shabaz123/easyL1105/easyl1105-sch-jpeg-rev1.jpg

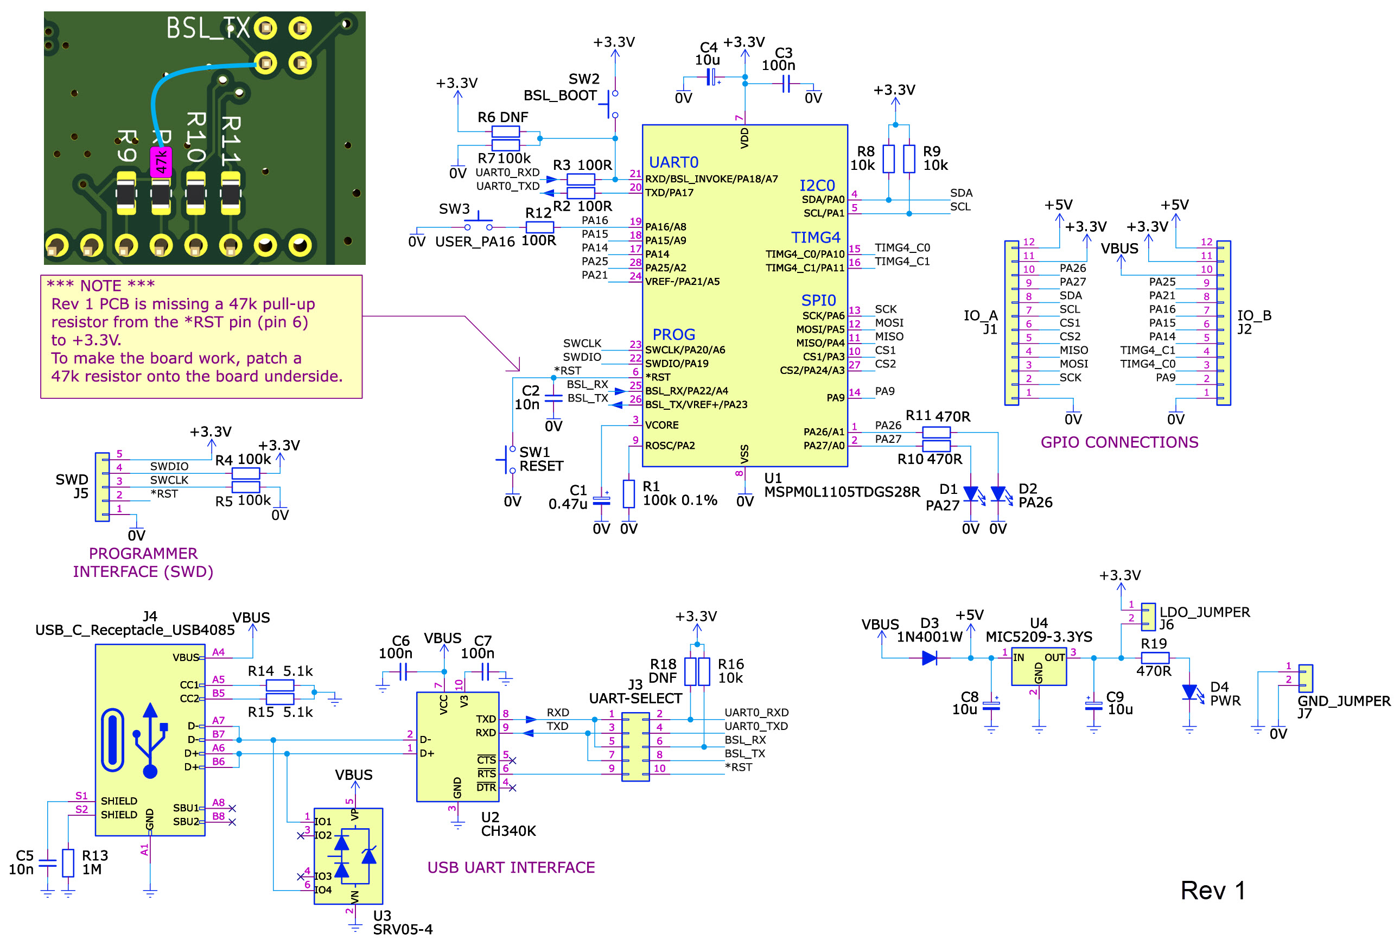
easyl1105-sch-jpeg-rev1.jpg
