shabaz123/easyL1105/msp-render-top.jpg

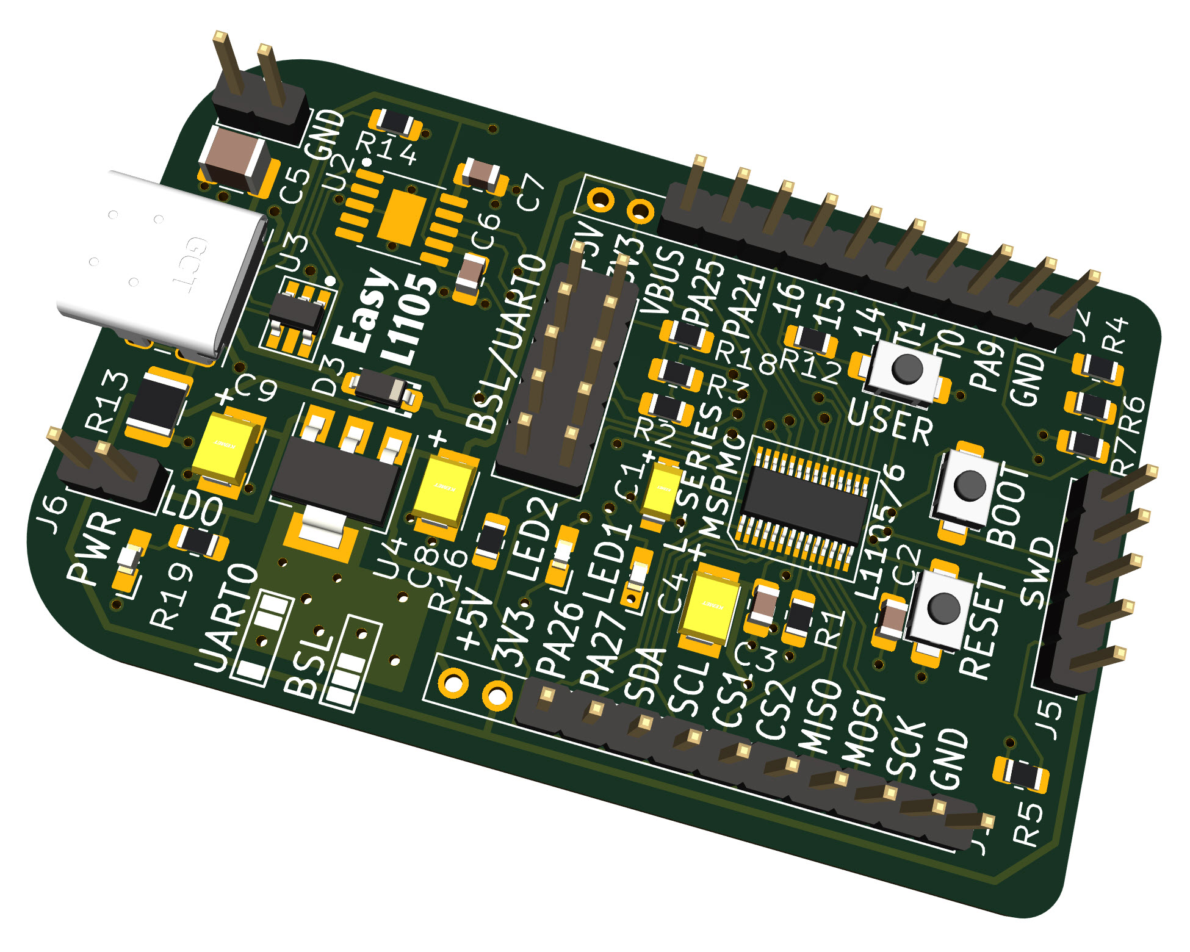
msp-render-top.jpg
